oskar456/poepi/PoEpi_v3/PoEpi_v3.png

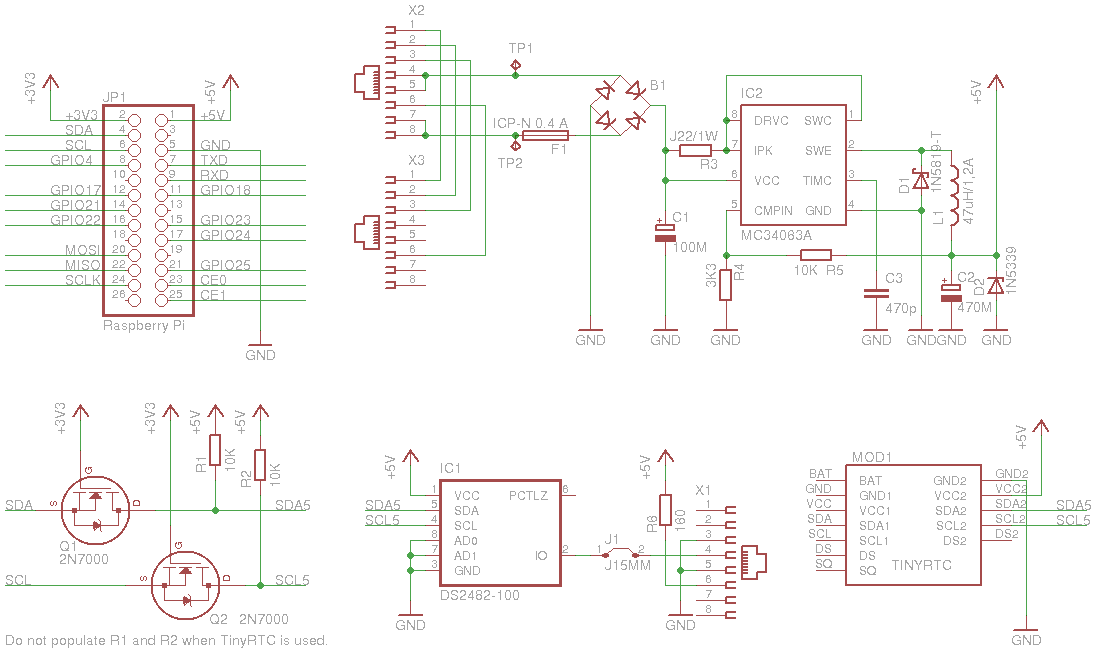
PoEpi_v3/PoEpi_v3.png
